MaxCraftx/Speaker-Enclosure-Design/renders_test/view_right.png

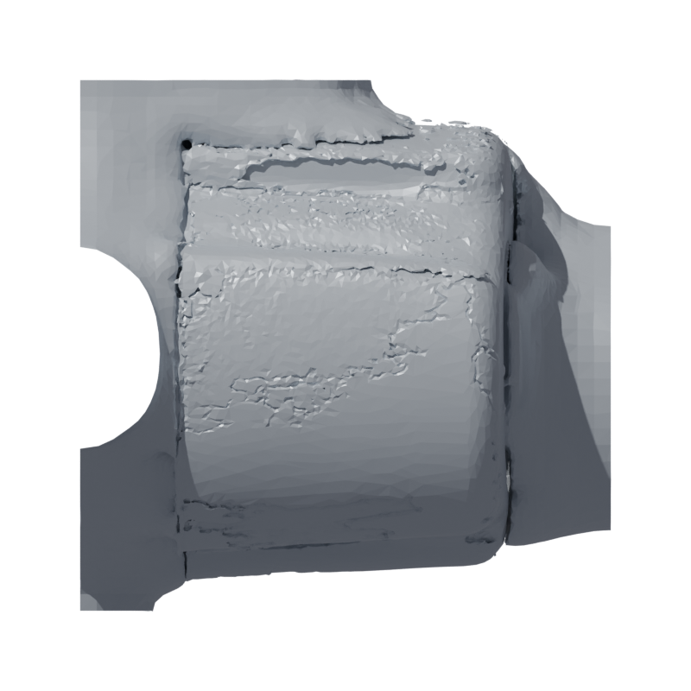
renders_test/view_right.png
